Alan-Lomax/MaxDuino/R1.6 (With RJ45)/Images/MaxDuino R1.6 PCB 3D.png

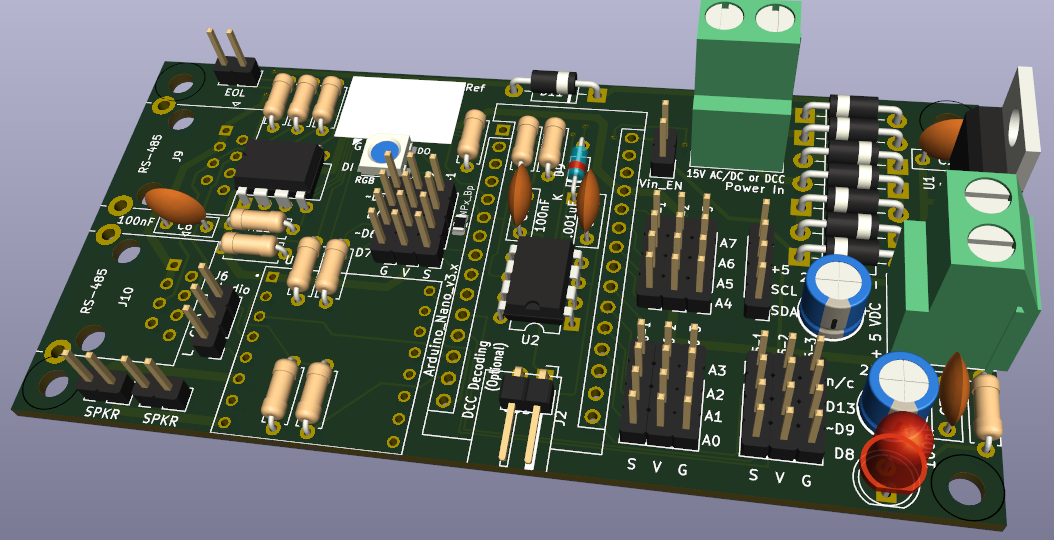
R1.6 (With RJ45)/Images/MaxDuino R1.6 PCB 3D.png
