Alan-Lomax/MaxDuino/R1.6 (With RJ45)/Images/MaxDuino R1.6 SCH.png

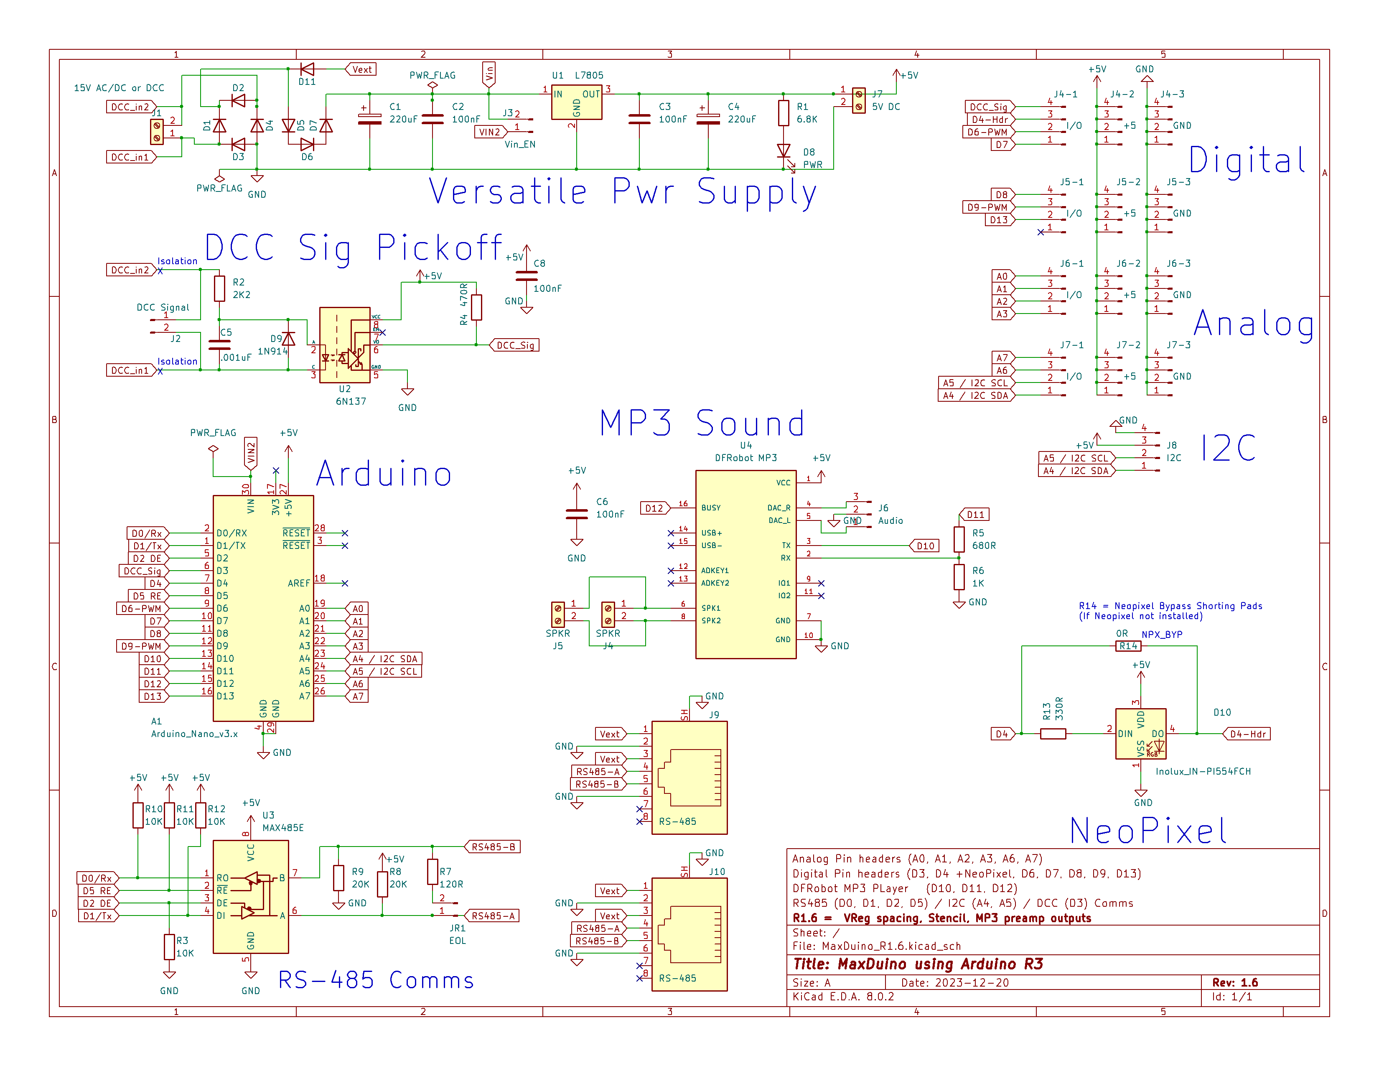
R1.6 (With RJ45)/Images/MaxDuino R1.6 SCH.png
