Alan-Lomax/MaxDuino/R1.6 (With RJ45)/Images/MAxduino V1.6 3D View of PCB (annotated).JPG

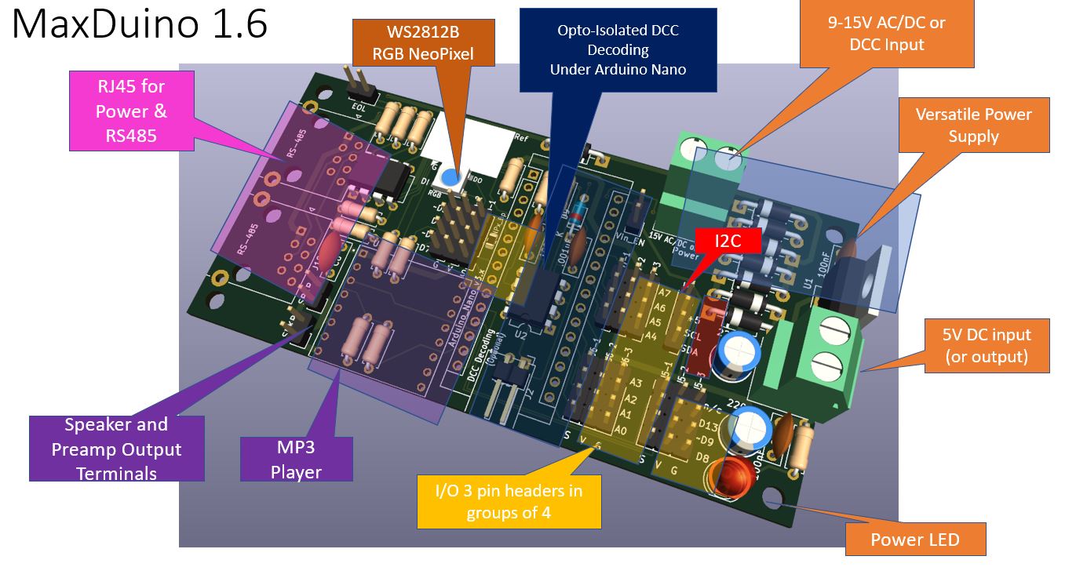
R1.6 (With RJ45)/Images/MAxduino V1.6 3D View of PCB (annotated).JPG
