Alan-Lomax/MaxDuino/R1.6 (With RJ45)/R1.6 Example Sketches/MaxDuino_RS485_MP3_R1.3/Screen Shots/00 JMRI-CMRI Connection Preferences.JPG

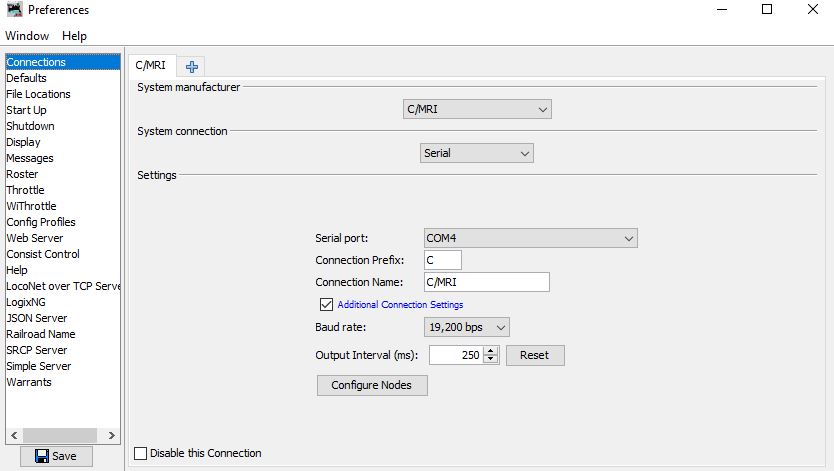
R1.6 (With RJ45)/R1.6 Example Sketches/MaxDuino_RS485_MP3_R1.3/Screen Shots/00 JMRI-CMRI Connection Preferences.JPG
