Alan-Lomax/MaxDuino/MaxDuino Resources/Construction Photos/04 MaxDuino Power Supply.png

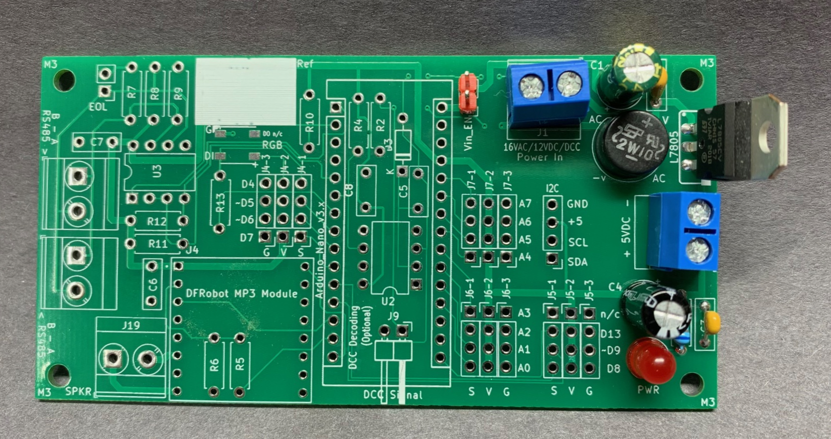
MaxDuino Resources/Construction Photos/04 MaxDuino Power Supply.png
