Alan-Lomax/MaxDuino/MaxDuino Resources/Construction Photos/05 MaxDuino DCC Decoder Circuitry.png

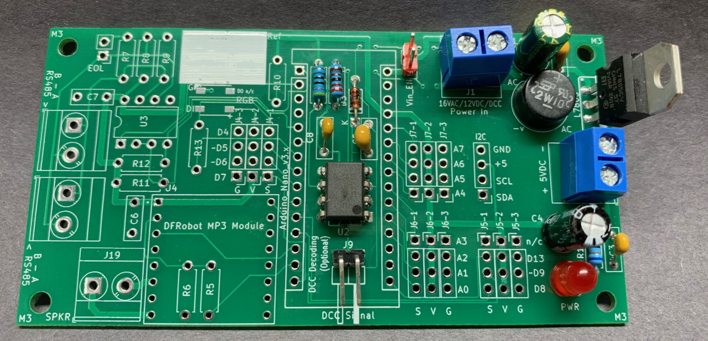
MaxDuino Resources/Construction Photos/05 MaxDuino DCC Decoder Circuitry.png
