Alan-Lomax/MaxDuino/MaxDuino Resources/Construction Photos/06 MaxDuino Header Pins Ready to Install.png

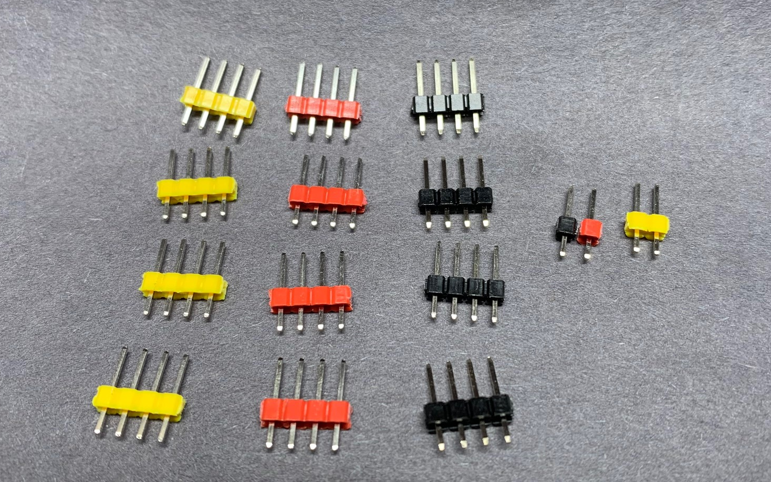
MaxDuino Resources/Construction Photos/06 MaxDuino Header Pins Ready to Install.png
