Alan-Lomax/MaxDuino/MaxDuino Resources/Construction Photos/09 MaxDuino Header Pins Fully Installed.png

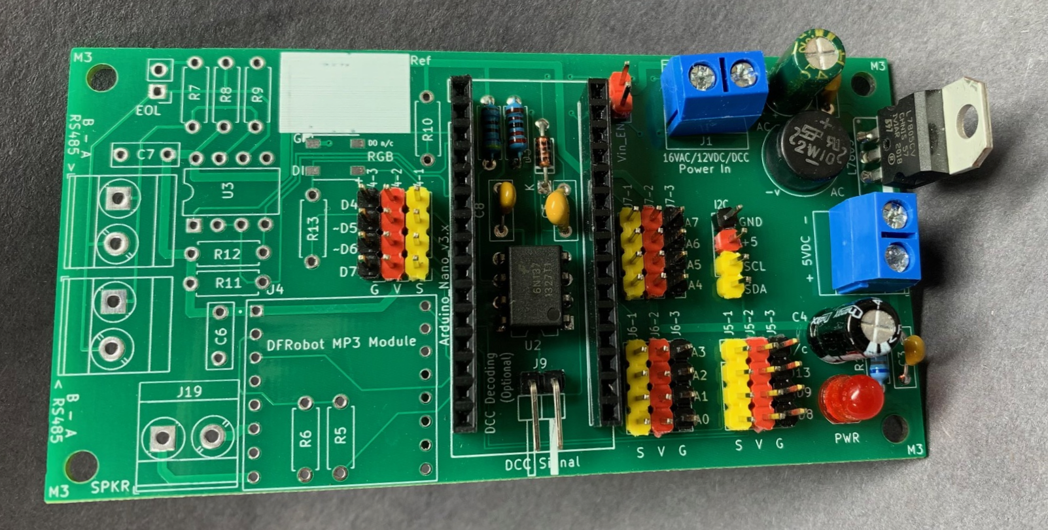
MaxDuino Resources/Construction Photos/09 MaxDuino Header Pins Fully Installed.png
