Alan-Lomax/MaxDuino/MaxDuino Resources/Construction Photos/10 MaxDuino with Arduino Installed and Powered.png

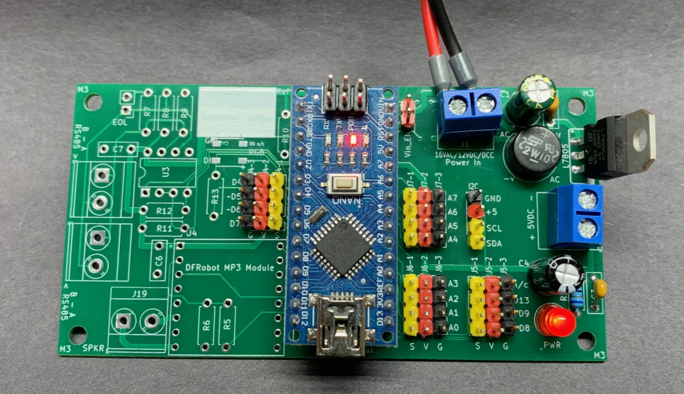
MaxDuino Resources/Construction Photos/10 MaxDuino with Arduino Installed and Powered.png
