Alan-Lomax/MaxDuino/MaxDuino Resources/Construction Photos/11 MaxDuino with MP3 Module Installed.png

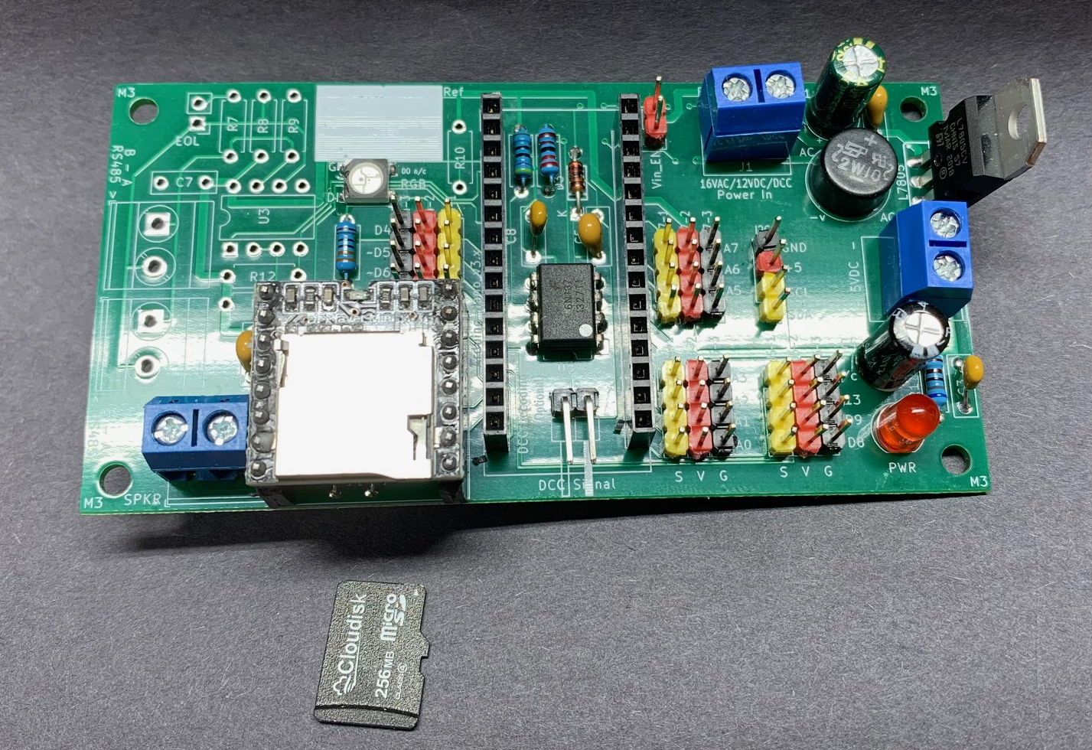
MaxDuino Resources/Construction Photos/11 MaxDuino with MP3 Module Installed.png
