Alan-Lomax/MaxDuino/MaxDuino Resources/Construction Photos/20 MaxDuino Small Speaker for MP3 Player.png

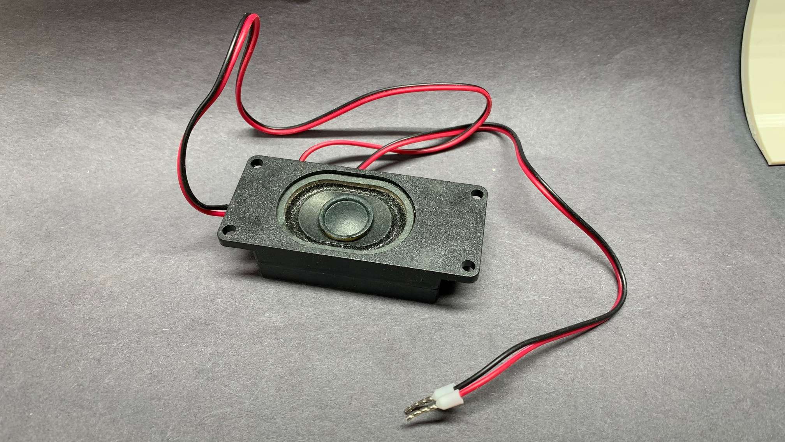
MaxDuino Resources/Construction Photos/20 MaxDuino Small Speaker for MP3 Player.png
