Alan-Lomax/MaxDuino/MaxDuino Resources/Construction Photos/23 MaxDuino Small OLED Display for I2C Test.png

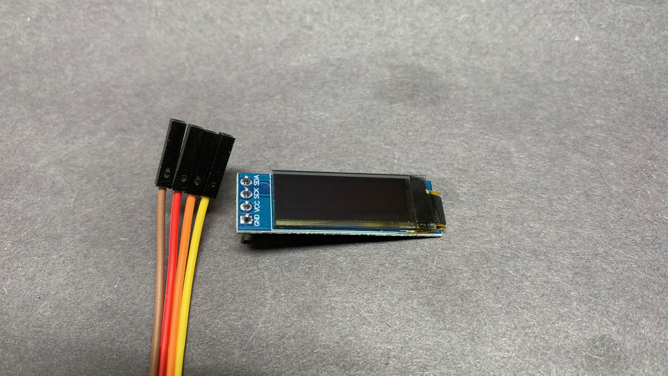
MaxDuino Resources/Construction Photos/23 MaxDuino Small OLED Display for I2C Test.png
