Alan-Lomax/MaxDuino/MaxDuino Resources/Construction Photos/24 MaxDuino IR Sensor forTesting header pins.png

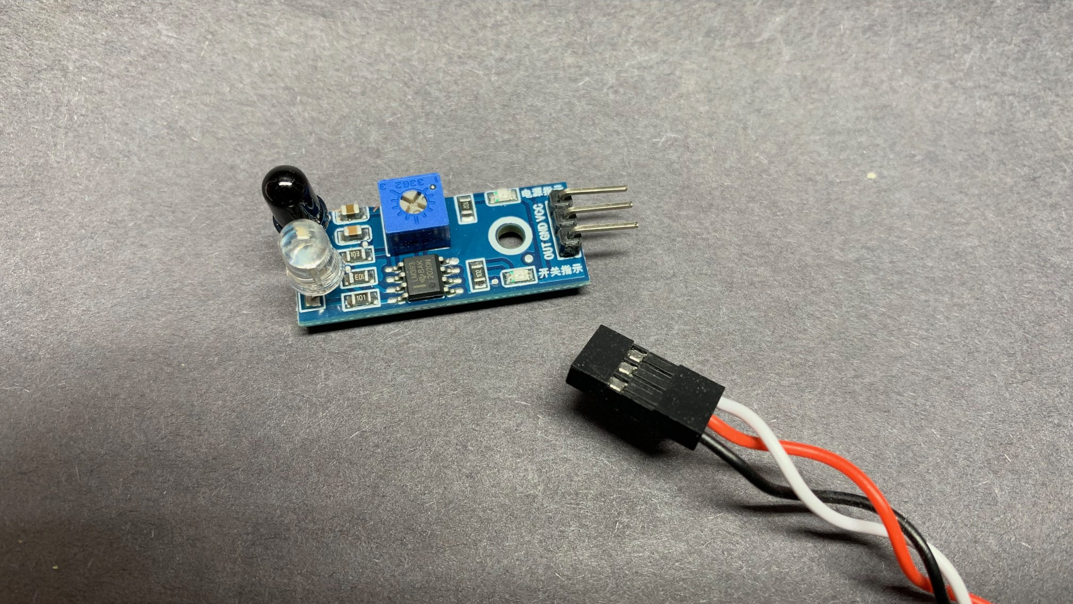
MaxDuino Resources/Construction Photos/24 MaxDuino IR Sensor forTesting header pins.png
