Alan-Lomax/MaxDuino/R1.6 (With RJ45)/R1.6 Example Sketches/MaxDuino_MP3_Sound_Check_R1.3/dfplayer_error_code_definitions.h

//
// DfPlayer Error Codes
//
#define TimeOut 0
#define WrongStack 1
#define DFPlayerCardInserted 2
#define DFPlayerCardRemoved 3
#define DFPlayerCardOnline 4
#define DFPlayerPlayFinished 5
#define DFPlayerError 6
#define DFPlayerUSBInserted 7
#define DFPlayerUSBRemoved 8
#define DFPlayerUSBOnline 9
#define DFPlayerCardUSBOnline 10
#define DFPlayerFeedBack 11

#define Busy 1
#define Sleeping 2
#define SerialWrongStack 3
#define CheckSumNotMatch 4
#define FileIndexOut 5
#define FileMismatch 6
#define Advertise 7

#define Stack_Header 0
#define Stack_Version 1
#define Stack_Length 2
#define Stack_Command 3
#define Stack_ACK 4
#define Stack_Parameter 5
#define Stack_CheckSum 7
#define Stack_End 9
